jmnich/ZeroCrossingDetector/sim.asc

D1: schottky; BAT54
R1: res; {RFB}
R2: res; 4.7k
R3: res; 1Meg
R4: res; 100k
R5: res; 100R
U1: AD8041
V1: voltage; 5V
V2: voltage; 5V
V3: voltage; SINE(0 1 5Meg 0 0 0)
V4: voltage; SINE(0 0 10000 0 0 0)
Named nets: 0, +5V, -5V, OUT, IN
.tran 0 25u 0 startup
.step param RFB list 47k 100k 100Meg
